doctea/usb_midi_clocker_hardware/expander_gate_output/expander_gate_output rear.png

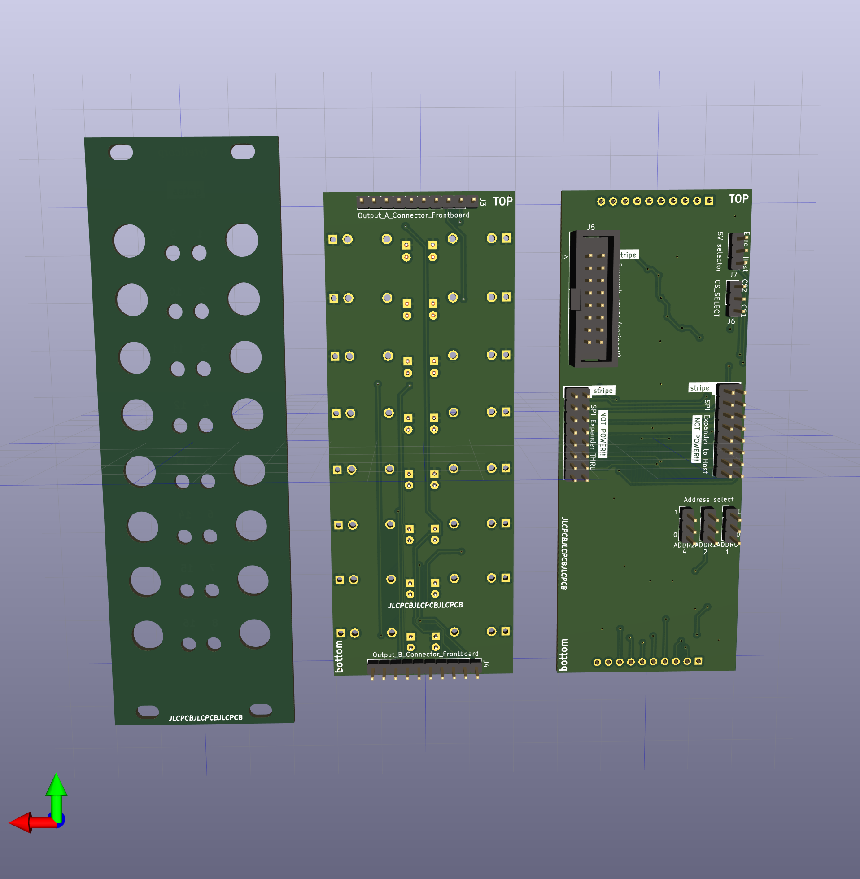
expander_gate_output/expander_gate_output rear.png
