doctea/usb_midi_clocker_hardware/expander_midi/expander_midi rear.png

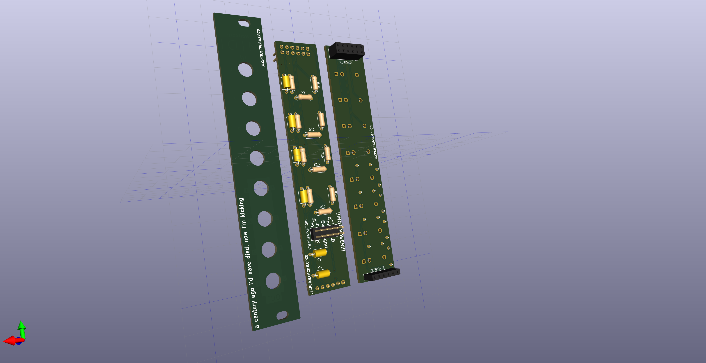
expander_midi/expander_midi rear.png
